Jacob-Lundstrom/jlcpcb-flex-rf/readme images/Schematic Sim results.png

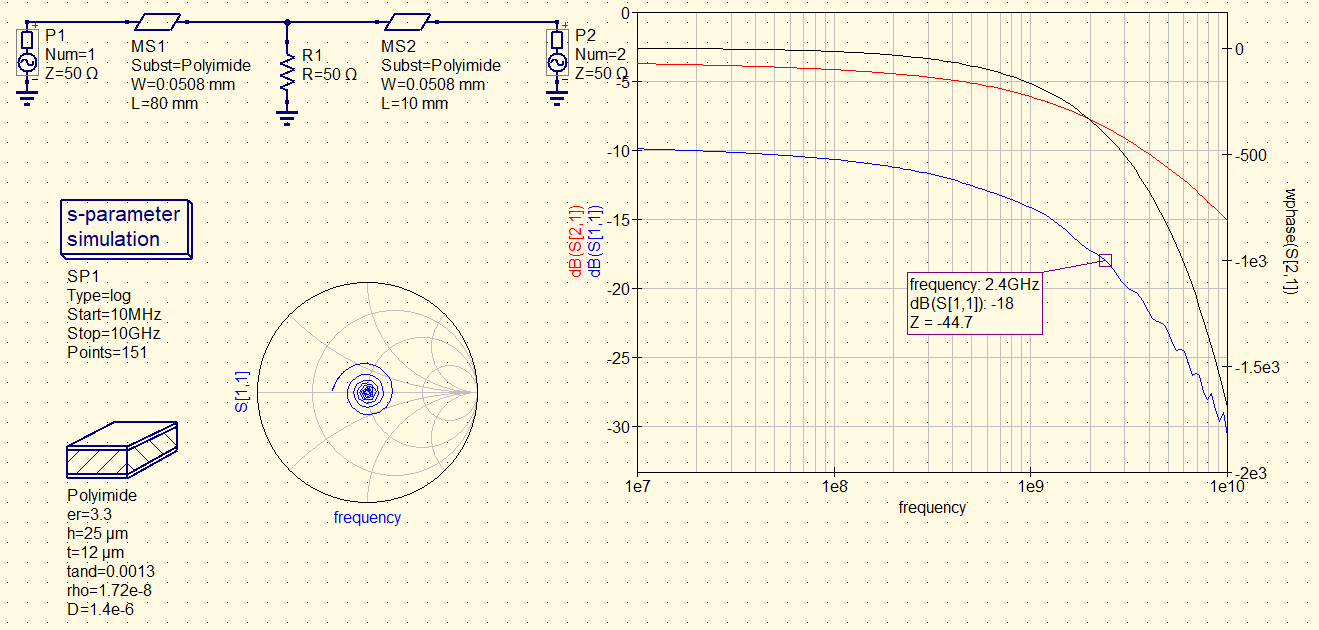
readme images/Schematic Sim results.png
