Jacob-Lundstrom/jlcpcb-flex-rf/simulation results/JLCPCB minimum trace width/sim sch.png

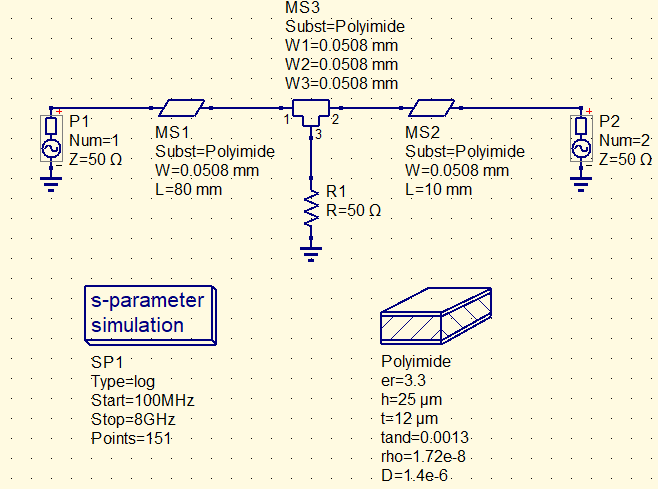
simulation results/JLCPCB minimum trace width/sim sch.png
