Jacob-Lundstrom/jlcpcb-flex-rf/test results/board 1/3 Mil, No Coverlay, Antenna/B1-3M-NC-A.bmp

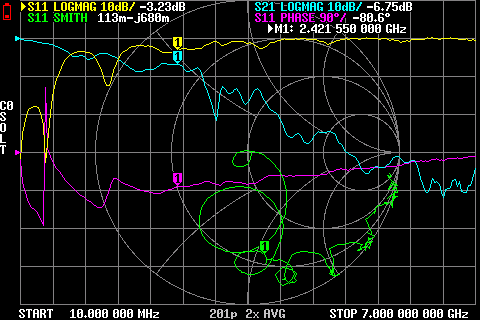
test results/board 1/3 Mil, No Coverlay, Antenna/B1-3M-NC-A.bmp
