Jacob-Lundstrom/jlcpcb-flex-rf/test results/board 1/3 Mil, Yes Coverlay, Antenna/B1-3M-YC-A.bmp

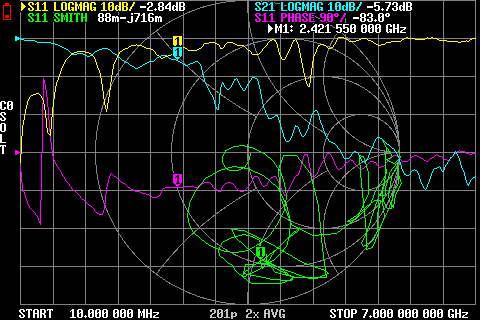
test results/board 1/3 Mil, Yes Coverlay, Antenna/B1-3M-YC-A.bmp
